particle-iot/snowflake/firmware/snowflake/src/audio_lib/rl6548_eq_table.h

#pragma once

const int eq_44p1k_en_num = 0x05;
const int eq_48k_en_num = 0x05;
const int eq_8k_en_num = 0x05;
const int eq_16k_en_num = 0x05;
const int eq_param_44p1k[] = {
	0x02001235,
	0xfc01518b,
	0x01feb12d,
	0x03fed2d3,
	0xfe012a74,
	0x02000000,
	0xfc025f1a,
	0x01fdabc6,
	0x03fda0e6,
	0xfe02543a,
	0x02000000,
	0xfc04b360,
	0x01fb7603,
	0x03fb4ca0,
	0xfe0489fd,
	0x02008d29,
	0xfc0ac5e0,
	0x01f5dec1,
	0x03f65179,
	0xfe0909b9,
	0x02000000,
	0xfc147836,
	0x01ee150b,
	0x03eb87ca,
	0xfe11eaf5,

};
const int eq_param_48k[] = {
	0x020010bb,
	0xfc0135f3,
	0x01fecc59,
	0x03feeb79,
	0xfe01123b,
	0x02000000,
	0xfc022d11,
	0x01fddc1d,
	0x03fdd2ef,
	0xfe0223e3,
	0x02000000,
	0xfc044ee9,
	0x01fbd40a,
	0x03fbb117,
	0xfe042bf6,
	0x020081c8,
	0xfc09db8a,
	0x01f6af8a,
	0x03f72587,
	0xfe084f42,
	0x02000000,
	0xfc12a480,
	0x01ef83bc,
	0x03ed5b80,
	0xfe107c44,

};
const int eq_param_8k[] = {
	0x02000000,
	0xfc16d09c,
	0x01ec47ef,
	0x03e92f64,
	0xfe13b811,
	0x02000000,
	0xfc32d2dd,
	0x01d94e9d,
	0x03cd2d23,
	0xfe26b163,
	0x02000000,
	0xfc53aeb7,
	0x01c7096e,
	0x03ac5149,
	0xfe38f692,
	0x02000000,
	0xfda2c2d4,
	0x0157efe8,
	0x025d3d2c,
	0xfea81018,
	0x02000000,
	0xfed149c5,
	0x0117062f,
	0x012eb63b,
	0xfee8f9d1,

};
const int eq_param_16k[] = {
	0x0000bf68,
	0x03fffff8,
	0x02000007,
	0x03c72f58,
	0xfe35d308,
	0x021d6453,
	0xfc6de63f,
	0x01b5c253,
	0x03c69354,
	0xfe13b811,
	0x023da05a,
	0xfd26baeb,
	0x016d15dc,
	0x03310c35,
	0xfe295859,
	0x02000000,
	0xfed149c5,
	0x0117062f,
	0x012eb63b,
	0xfee8f9d1,
	0x02000000,
	0xff6b511a,
	0x00fa1ffd,
	0x0094aee6,
	0xff05e003,

};
